mrstefangrimm/Parc/Hardware/Soldering-Scheme-FeatherStack.jpeg

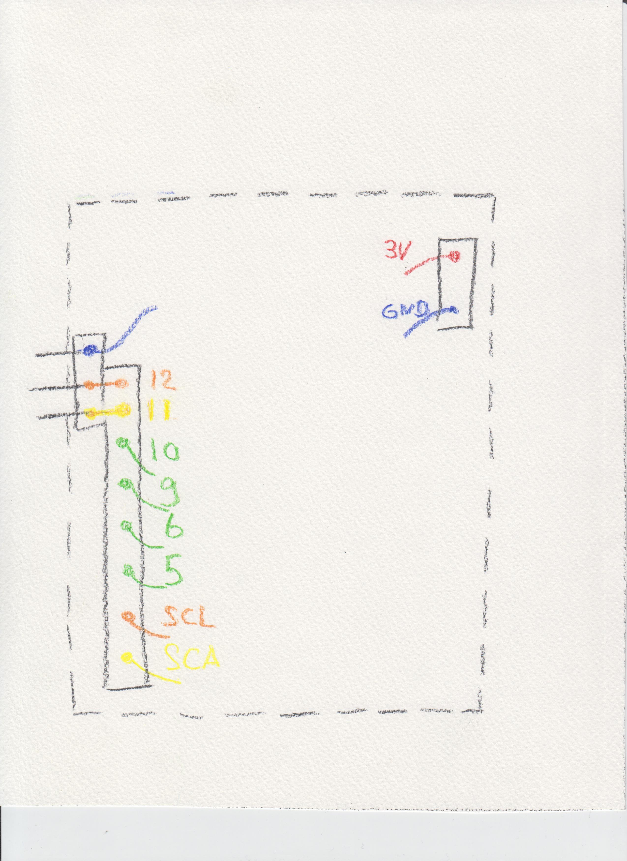
Hardware/Soldering-Scheme-FeatherStack.jpeg
