mrstefangrimm/Parc/Hardware/Soldering-Scheme-Keypad.jpeg

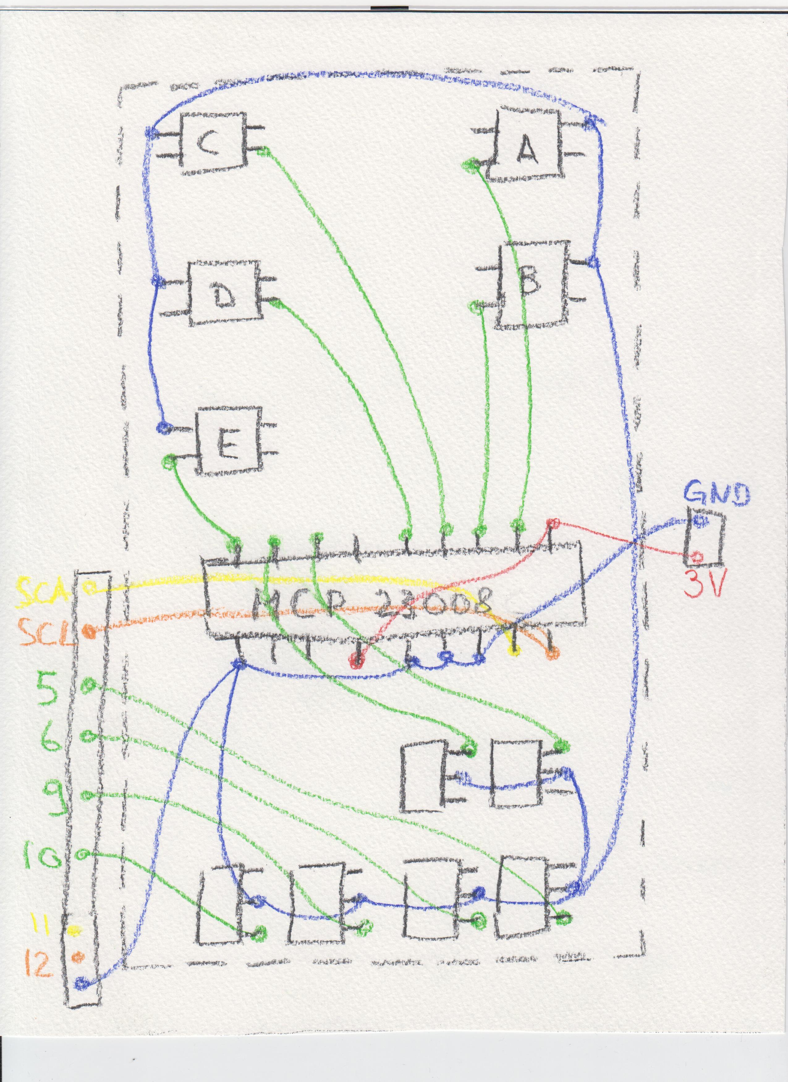
Hardware/Soldering-Scheme-Keypad.jpeg
