mrstefangrimm/Parc/Software/Src/UnoParcApp/Constants.h

// Copyright (c) 2021 Stefan Grimm. All rights reserved.
// Licensed under the LGPL. See LICENSE file in the project root for full license information.
//
#pragma once

namespace unoparc {

// Constants to avoids multiple usage of GPIOs.
// No additional memory is used because of the external constants.

const uint8_t Pin_A = 10;
const uint8_t Pin_B = 9;
const uint8_t Pin_C = 8;
const uint8_t Pin_D = 7;
const uint8_t Pin_E = 6;
const uint8_t Pin_M0 = 5;
const uint8_t Pin_M1 = 0;

const uint8_t Pin_C0 = 0;
const uint8_t Pin_C1 = 0;
const uint8_t Pin_C2 = 0;
const uint8_t Pin_C3 = 0;

const uint8_t Usb_YEL = 11;
const uint8_t Usb_ORA = 12;

}
