mrstefangrimm/Parc/Software/Src/ParcLib/Core/TerminalAo.h

// Copyright (c) 2021-2023 Stefan Grimm. All rights reserved.
// Licensed under the LGPL. See LICENSE file in the project root for full license information.
//
#ifndef PARCLIB_TERMINALAO_H
#define PARCLIB_TERMINALAO_H

#include "Ao.h"
#include "StringParc.h"
#include "Shared.h"
#include "tsm.h"

namespace parclib {

enum PsType {
  Wait,
  UsbKeycode,
  UsbKeycodeRepeated,
  UsbKeycodes,
  UsbText,
  BleKeycode,
  BleKeycodeRepeated,
  BleText,
  BleControlkey
};

enum CmdType {
  _LastStep = BleControlkey,
  Pin
};

template<uint8_t CMDTYPE>
struct CmdComparator {

  bool operator()(const char* another) const {
    return equals(another);
  }
  bool equals(const char* another) const {
    return false;
  }

  bool operator()(char** another) const {
    return equals(another);
  }
  bool equals(char** another) const {
    return false;
  }

};

template<class PROGSTEPFACTORY, class TLOGGERFAC, class KNOWNKEYCODES>
class ProgramStepCreator {
public:
  static ProgramStep<TLOGGERFAC>* createProgramStepWait(const char* delay) {
    uint16_t waitMs = atoi(delay);
    // Debug: _log.print(F("Delay: ")); _log.println(waitMs);

    auto log = TLOGGERFAC::create();
    log->println(F("Create Wait_t"));
    return new Wait_t(waitMs);
  }

  static ProgramStep<TLOGGERFAC>* createProgramStepBleKeyboardCode(char* subStrs[], uint8_t numSubStr) {
    KeyCode keyCode;
    uint8_t repetitions = 0;
    for (int n = 1; n < numSubStr; n++) {
      keyCode.ctrl |= strcmp(subStrs[n], "<Ctrl>") == 0;
      keyCode.shift |= strcmp(subStrs[n], "<Shift>") == 0;
      keyCode.alt |= strcmp(subStrs[n], "<Alt>") == 0;
      keyCode.win |= strcmp(subStrs[n], "<Win>") == 0;

      if (strcmp2("-r", subStrs[n][0], subStrs[n][1])) {
        repetitions = atoi(&subStrs[n][2]);
      }
    }

    auto code = subStrs[numSubStr - 1];
    keyCode.hexCode = strtol(subStrs[numSubStr - 1], 0, KNOWNKEYCODES::BleRadix);
    if (keyCode.hexCode == 0) {
      keyCode.hexCode = symbolToBleKeyode(code);
    }
    auto log = TLOGGERFAC::create();
    //log.print("ProgramStepBleKeyboardCode "); _log.print(hexCode, HEX);
    if (repetitions == 0) {
      log->println(F("Create BleKeycode_t"));
      return new BleKeycode_t(keyCode);
    }
    log->println(F("Create BleKeycodeRepeated_t"));
    return new BleKeycodeRepeated_t(keyCode, repetitions);
  }

  static ProgramStep<TLOGGERFAC>* createProgramStepBleKeyboardText(char* text) {
    auto log = TLOGGERFAC::create();
    //_log.print("TEXT: "); _log.println(text);
    log->println(F("Create BleText_t"));
    return new BleText_t(text);
  }

  static ProgramStep<TLOGGERFAC>* createProgramStepBleControlKey(char* subStrs[], uint8_t numSubStr) {
    auto log = TLOGGERFAC::create();
    // _log.print("Control Key: "); _log.print(subStrs[1]);

    if (strcmp(subStrs[1], "Volume+") == 0) {
      return new BleControlkey_t("0xE9");
    }
    if (strcmp(subStrs[1], "Volume-") == 0) {
      return new BleControlkey_t("0xEA");
    }

    log->println(F("Create BleControlkey_t"));
    return new BleControlkey_t(subStrs[1]);
  }

  static ProgramStep<TLOGGERFAC>* createProgramStepUsbKeyboardCode(char* subStrs[], uint8_t numSubStr) {
    KeyCode keyCode;
    uint8_t repetitions = 0;
    char second = 0;
    for (int n = 1; n < numSubStr; n++) {
      keyCode.ctrl |= strcmp(subStrs[n], "<Ctrl>") == 0;
      keyCode.shift |= strcmp(subStrs[n], "<Shift>") == 0;
      keyCode.alt |= strcmp(subStrs[n], "<Alt>") == 0;
      keyCode.win |= strcmp(subStrs[n], "<Win>") == 0;

      if (strcmp2("-r", subStrs[n][0], subStrs[n][1])) {
        repetitions = atoi(&subStrs[n][2]);
      }
    }

    auto code = subStrs[numSubStr - 1];
    auto log = TLOGGERFAC::create();
    //Debug: _log.print("createProgramStepUsbKeyboardCode "); _log.println(code);

    if (strlen(code) == 3) {
      if (code[0] == '\'' && code[2] == '\'') {
        keyCode.hexCode = code[1];
      }
      else if (repetitions == 0) {
        keyCode.hexCode = code[0];
        second = code[2];
      }
    }
    else {
      keyCode.hexCode = strtol(code, 0, KNOWNKEYCODES::UsbRadix);
    }
    //Debug: _log.print("createProgramStepUsbKeyboardCode "); _log.println(keyCode.hexCode, HEX);
    if (keyCode.hexCode == 0) {
      keyCode.hexCode = symbolToUsbKeyode(code);
    }
    //Debug: _log.print("createProgramStepUsbKeyboardCode "); _log.println(keyCode.hexCode, HEX);
    if (second != 0) {
      log->println(F("Create UsbKeycodes_t"));
      return new UsbKeycodes_t(keyCode, second);
    }
    if (repetitions == 0) {
      log->println(F("Create UsbKeycode_t"));
      return new UsbKeycode_t(keyCode);
    }
    log->println(F("Create UsbKeycodeRepeated_t"));
    return new UsbKeycodeRepeated_t(keyCode, repetitions);
  }

  static ProgramStep<TLOGGERFAC>* createProgramStepUsbKeyboardText(char* text) {
    auto log = TLOGGERFAC::create();
    // log.print("TEXT: "); _log.println(text);
    log->println(F("Create UsbText_t"));
    return new UsbText_t(text);
  }

private:
  using Wait_t = typename TypeAt<PROGSTEPFACTORY, PsType::Wait>::Result;
  using UsbKeycode_t = typename TypeAt<PROGSTEPFACTORY, PsType::UsbKeycode>::Result;
  using UsbKeycodeRepeated_t = typename TypeAt<PROGSTEPFACTORY, PsType::UsbKeycodeRepeated>::Result;
  using UsbKeycodes_t = typename TypeAt<PROGSTEPFACTORY, PsType::UsbKeycodes>::Result;
  using UsbText_t = typename TypeAt<PROGSTEPFACTORY, PsType::UsbText>::Result;
  using BleKeycode_t = typename TypeAt<PROGSTEPFACTORY, PsType::BleKeycode>::Result;
  using BleKeycodeRepeated_t = typename TypeAt<PROGSTEPFACTORY, PsType::BleKeycodeRepeated>::Result;
  using BleText_t = typename TypeAt<PROGSTEPFACTORY, PsType::BleText>::Result;
  using BleControlkey_t = typename TypeAt<PROGSTEPFACTORY, PsType::BleControlkey>::Result;

  static uint8_t symbolToUsbKeyode(const char* code) {
    if (strcmp(code, "<Del>") == 0) {
      return KNOWNKEYCODES::UsbKeyCodeDel;
    }
    if (strcmp(code, "<Tab>") == 0) {
      return KNOWNKEYCODES::UsbKeyCodeTab;
    }
    if (strcmp(code, "<Enter>") == 0) {
      return KNOWNKEYCODES::UsbKeyCodeEnter;
    }
    if (strcmp(code, "<Space>") == 0) {
      return KNOWNKEYCODES::UsbKeyCodeSpace;
    }
    return 0;
  }

  static uint8_t symbolToBleKeyode(const char* code) {
    if (strcmp(code, "<Del>") == 0) {
      return KNOWNKEYCODES::BleKeyCodeDel;
    }
    if (strcmp(code, "<Tab>") == 0) {
      return KNOWNKEYCODES::BleKeyCodeTab;
    }
    if (strcmp(code, "<Enter>") == 0) {
      return KNOWNKEYCODES::BleKeyCodeEnter;
    }
    if (strcmp(code, "<Space>") == 0) {
      return KNOWNKEYCODES::BleKeyCodeSpace;
    }
    return 0;
  }

};

using StatePolicy = tsmlib::State<tsmlib::MemoryAddressComparator, true>;

namespace Trigger {
  struct Timeout {
    void* owner;
  };
  struct InvalidData {
  };
  struct GotPin {
    void* owner;
  };
  struct GotProgramSteps {
    void* owner;
  };
}

// https://viewer.diagrams.net/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

template<class PROGSTEPFACTORY, class TSERIAL, class TLOGGERFAC, class THIDBLEFAC, class THIDUSBFAC, class TPROGRAM, class TSYSTEMHWFAC, class KNOWNKEYCODES, uint8_t BUFLEN>
class TerminalAo : public Ao<TerminalAo<PROGSTEPFACTORY, TSERIAL, TLOGGERFAC, THIDBLEFAC, THIDUSBFAC, TPROGRAM, TSYSTEMHWFAC, KNOWNKEYCODES, BUFLEN>> {

  using Ao_t = Ao<TerminalAo<PROGSTEPFACTORY, TSERIAL, TLOGGERFAC, THIDBLEFAC, THIDUSBFAC, TPROGRAM, TSYSTEMHWFAC, KNOWNKEYCODES, BUFLEN>>;

public:
  TerminalAo(TSERIAL& serialInput, Messages& messages, TPROGRAM* programs)
    : Ao_t(messages), _serial(serialInput), _programs(programs) {
    _statemachine.begin();
  }

  void load() {
    if (_timer.increment()) {
      _msg = TerminalData(Ao_t::_messages.toTerminalQueue.pop());
    }
  }

  void run() {
    if (_timer.current())
    {
      if (_msg.raw == 0 || _msg.isPinMessage) {
        _statemachine.dispatch(Trigger::Timeout{ this });
      }
      else {
        if (_msg.invalidProgramCode)
        {
          _statemachine.dispatch(Trigger::InvalidData{});
        }
        else if (_msg.gotPin)
        {
          _statemachine.dispatch(Trigger::GotPin{ this });
        }
        else if (_msg.gotProgramSteps)
        {
          _statemachine.dispatch(Trigger::GotProgramSteps{ this });
        }
      }

      if (_msg.isPinMessage && _msg.isPinDefined) {
        _serial.println(F("PIN was not accepted. A PIN is already active."));
      }

      _msg = TerminalData();
    }
  }

protected:
  // states
  struct Idle : public tsmlib::BasicState<Idle, StatePolicy, true, false, true>, public tsmlib::SingletonCreator<Idle> {

    bool gotProgramCode = false;

    template<class Event> void entry(const Event&) {
      gotProgramCode = false;
    }

    template<class Event> void doit(const Event& ev) { doit(ev, Identity<Event>()); }
    template<class Event> void doit(const Event&, Identity<Event>) {}
    void doit(const Trigger::Timeout& ev, Identity<Trigger::Timeout>) {
      auto ao = static_cast<TerminalAo*>(ev.owner);
      gotProgramCode = ao->onStateIdleDo();
    }
  };

  struct ReadingProgramCode : public tsmlib::BasicState<ReadingProgramCode, StatePolicy, true, false, true>, public tsmlib::SingletonCreator<ReadingProgramCode> {

    template<class Event> void entry(const Event& ev) { entry(ev, Identity<Event>()); }
    template<class Event> void entry(const Event&, Identity<Event>) {}
    void entry(const Trigger::Timeout& ev, Identity<Trigger::Timeout>) {
      auto ao = static_cast<TerminalAo*>(ev.owner);
      ao->clearReadBuffer();
    }

    template<class Event> void doit(const Event& ev) { doit(ev, Identity<Event>()); }
    template<class Event> void doit(const Event&, Identity<Event>) {}
    void doit(const Trigger::Timeout& ev, Identity<Trigger::Timeout>) {
      auto ao = static_cast<TerminalAo*>(ev.owner);
      ao->onStateReadingProgramCodeDo();
    }
  };

  struct ReadingProgramSteps : public tsmlib::BasicState<ReadingProgramSteps, StatePolicy, true, false, true>, public tsmlib::SingletonCreator<ReadingProgramSteps> {

    bool readingDone = false;

    template<class Event> void entry(const Event& ev) {
      readingDone = false;
      entry(ev, Identity<Event>());
    }
    template<class Event> void entry(const Event&, Identity<Event>) {}
    void entry(const Trigger::GotProgramSteps& ev, Identity<Trigger::GotProgramSteps>) {
      auto ao = static_cast<TerminalAo*>(ev.owner);
      ao->clearReadBuffer();
    }

    template<class Event> void doit(const Event& ev) { doit(ev, Identity<Event>()); }
    template<class Event> void doit(const Event&, Identity<Event>) {}
    void doit(const Trigger::Timeout& ev, Identity<Trigger::Timeout>) {
      auto ao = static_cast<TerminalAo*>(ev.owner);
      readingDone = ao->onStateReadingProgramStepsOnDo();
    }
  };

  struct ReadingPin : public tsmlib::BasicState<ReadingPin, StatePolicy, true, false, true>, public tsmlib::SingletonCreator<ReadingPin> {

    bool readingDone = false;

    template<class Event> void entry(const Event& ev) {
      readingDone = false;
      entry(ev, Identity<Event>());
    }
    template<class Event> void entry(const Event&, Identity<Event>) {}
    void entry(const Trigger::GotPin& ev, Identity<Trigger::GotPin>) {
      auto ao = static_cast<TerminalAo*>(ev.owner);
      ao->clearReadBuffer();
    }

    template<class Event> void doit(const Event& ev) { doit(ev, Identity<Event>()); }
    template<class Event> void doit(const Event&, Identity<Event>) {}
    void doit(const Trigger::Timeout& ev, Identity<Trigger::Timeout>) {
      auto ao = static_cast<TerminalAo*>(ev.owner);
      readingDone = ao->onStateReadingPinDo();
    }
  };

  // guards
  struct ToReadingProgramCodeFromIdleGuard {
    bool eval(const Idle& idle, const Trigger::Timeout&) {
      return idle.gotProgramCode;
    }
  };

  struct ToIdleFromReadingProgramStepsGuard
  {
    bool eval(const ReadingProgramSteps& readingProgramSteps, const Trigger::Timeout&) {
      return readingProgramSteps.readingDone;
    }
  };

  struct ToIdleFromReadingPinGuard
  {
    bool eval(const ReadingPin& readingPin, const Trigger::Timeout&) {
      return readingPin.readingDone;
    }
  };

  using ToReadingProgramCodeFromIdle = tsmlib::ChoiceTransition<Trigger::Timeout, ReadingProgramCode, Idle, Idle, ToReadingProgramCodeFromIdleGuard, tsmlib::NoAction>;
  using ToReadingProgramCodeFromReadingProgramCode = tsmlib::SelfTransition<Trigger::Timeout, ReadingProgramCode, tsmlib::NoGuard, tsmlib::NoAction, false>;
  using ToReadingPinFromReadingProgramCode = tsmlib::Transition<Trigger::GotPin, ReadingPin, ReadingProgramCode, tsmlib::NoGuard, tsmlib::NoAction>;
  using ToReadingProgramStepsFromProgramCode = tsmlib::Transition<Trigger::GotProgramSteps, ReadingProgramSteps, ReadingProgramCode, tsmlib::NoGuard, tsmlib::NoAction>;
  using ToIdleFromProgramCode = tsmlib::Transition<Trigger::InvalidData, Idle, ReadingProgramCode, tsmlib::NoGuard, tsmlib::NoAction>;

  using ToIdleFromReadingProgramSteps = tsmlib::ChoiceTransition<Trigger::Timeout, Idle, ReadingProgramSteps, ReadingProgramSteps, ToIdleFromReadingProgramStepsGuard, tsmlib::NoAction>;
  using ToIdleFromReadingPin = tsmlib::ChoiceTransition<Trigger::Timeout, Idle, ReadingPin, ReadingPin, ToIdleFromReadingPinGuard, tsmlib::NoAction>;

  using Transitions =
    tsmlib::Typelist<ToReadingProgramCodeFromIdle,
    tsmlib::Typelist<ToReadingProgramCodeFromReadingProgramCode,
    tsmlib::Typelist<ToReadingPinFromReadingProgramCode,
    tsmlib::Typelist<ToReadingProgramStepsFromProgramCode,
    tsmlib::Typelist<ToIdleFromProgramCode,
    tsmlib::Typelist<ToIdleFromReadingProgramSteps,
    tsmlib::Typelist<ToIdleFromReadingPin,
    tsmlib::NullType>>>>>>>;

  // state machine
  using InitTransition = tsmlib::InitialTransition<Idle, tsmlib::NoAction>;
  using SM_t = tsmlib::Statemachine<Transitions, InitTransition>;
  SM_t _statemachine;

  TSERIAL& _serial;
  BitCounter<0> _timer;
  TerminalData _msg;

  bool onStateIdleDo() {
    char ch = 0;
    while (_serial.available()) {
      ch = _serial.read();
      if (ch == '{') {
        // send blocked to KeypadAo
        _serial.print(F("> {"));
        return true;
      }
      else if (ch == '?') {
        _serial.println(F("Programmed:"));
        for (int m = 0; m < 4; m++) {
          for (int n = 1; n < 6; n++) {
            KeypadRegData input(m, n);
            _serial.print(input.mode); _serial.print(F(" ")); _serial.print(char(input.button - 1 + 'A')); _serial.print(F(" : "));
            _programs[input.programIndex()].hasSteps() ? _serial.println(F("Yes")) : _serial.println(F("No"));
          }
        }
        auto sysHw = TSYSTEMHWFAC::create();
        _serial.print(F("Remaining bytes: ")); _serial.println(sysHw->freeMemory());
        return false;
      }
      else if (isprint(ch)) {
        _serial.print(ch);
      }
    }
    if (ch != 0 /*&& ch != 0b1101 && ch != 0b1010*/) {
      // YAT sends 0b1101 and 0b1010, PuTTY sends 0b1101 and powershell sends 0b1010
      // Debug: Serial.println("Enter pressed");
      // Debug: Serial.println(); //eol of repeated command
      _serial.println(F("Start defining your dull programs."));
    }
    return false;
  }

  void onStateReadingProgramCodeDo() {
    auto log = TLOGGERFAC::create();

    while (_serial.available()) {
      char ch = _serial.read();
      _serial.print(ch);
      if (ch == ':') {
        parclib::trimFront(_buf);
        parclib::trimBack(_buf, BUFLEN);
        parclib::squeeze(_buf);
        // Debug: _serial.println(_buf);
        uint8_t numSubStr;
        char* subStrs[2] = { 0 };
        parclib::split(_buf, BUFLEN, ' ', subStrs, &numSubStr);

        if (numSubStr == 2) {
          if (CmdComparator<CmdType::Pin>()(subStrs)) {
            _keyPadInput.isPin = 1;
          }
          else {
            // Debug: _serial.println(subStrs[0][0]); // Does not work when backspace is used in putty
            // Debug: _serial.println(subStrs[1][0]); // Does not work when backspace is used in putty
            // Debug: _serial.println(subStrs[0][strlen(subStrs[0])-1]);
            // Debug: _serial.println(subStrs[1][strlen(subStrs[1])-1]);

            _keyPadInput.isPin = 0;
            _keyPadInput.mode = subStrs[0][0] - '0';
            _keyPadInput.button = subStrs[1][0] - 'A' + 1;

            // Debug: _serial.println(_keyPadInput.mode);
            // Debug: _serial.println(_keyPadInput.button);
          }
        }

        if (_keyPadInput.isPin) {
          log->println(F("got pin"));
          TerminalData msg;
          msg.gotPin = true;
          Ao_t::_messages.toTerminalQueue.push(msg.raw);
          return;
        }
        auto idx = _keyPadInput.programIndex();
        // Debug: _log.print(_keyPadInput.mode); _log.print(F(" ")); _log.print(_keyPadInput.button); _log.print(F(" > ")); _log.println(idx);
        if (0 <= idx && idx < NumberOfPrograms) {
          TPROGRAM& prog = _programs[idx];
          if (prog.hasSteps()) {
            log->println(F("got program index. Current program is being disposed."));
          }
          prog.dispose();
          TerminalData msg;
          msg.gotProgramSteps = true;
          Ao_t::_messages.toTerminalQueue.push(msg.raw);
          return;
        }
        _serial.println(F(" This ain't dull, bye."));
        TerminalData msg;
        msg.invalidProgramCode = true;
        Ao_t::_messages.toTerminalQueue.push(msg.raw);
      }
      else if (_itBuf < BUFLEN) {
        // omit preceding spaces to save the buffer for the data.
        if (_itBuf > 0 || ch != ' ') {
          _buf[_itBuf] = ch;
          _itBuf++;
        }
      }
    }
  }

  bool onStateReadingPinDo() {
    // Debug:auto log = TLOGGERFAC::create();

    while (_serial.available()) {
      char ch = _serial.read();
      _serial.print(ch);
      // Debug: log->print(ch);

      if (ch == '}') {
        _serial.println(F(", thank you."));
        // Debug: log->println(F(", thank you."));

        return true;
        // send unblocked to KeypadAo
      }
      else if (ch == ';') {
        // create programstep. If failed, go to wait state
        // Debug: log->print(_buf);
        parclib::trimFront(_buf);
        parclib::trimBack(_buf, BUFLEN);
        parclib::squeeze(_buf);
        uint8_t numSubStr;
        char* subStrs[6] = { 0 };
        parclib::split(_buf, BUFLEN, ' ', subStrs, &numSubStr);

        if (numSubStr != 5) {
          _serial.println(F(" This ain't dull, bye."));
          // Debug: log->print(F(" This ain't dull, bye."));
          return true;
        }
        PinRegData pin;
        pin.code3 = subStrs[0][0] == '1' ? 1 : 0;
        pin.code2 = subStrs[1][0] == '1' ? 1 : 0;
        pin.code1 = subStrs[2][0] == '1' ? 1 : 0;
        pin.code0 = subStrs[3][0] == '1' ? 1 : 0;
        pin.retries = atoi(subStrs[4]);

        // Pin is sent before the command is completed with '}'
        Ao_t::_messages.fromTerminalToKeypadQueue.push(pin.raw);
      }
      else if (_itBuf < BUFLEN) {
        // omit preceding spaces to save the buffer for the data.
        if (_itBuf > 0 || ch != ' ') {
          _buf[_itBuf] = ch;
          _itBuf++;
        }
      }
    }
    return false;
  }

  bool onStateReadingProgramStepsOnDo() {
    while (_serial.available()) {
      char ch = _serial.read();
      _serial.print(ch);
      if (ch == '}') {
        _serial.println(F(", thank you."));
        Ao_t::_messages.fromTerminalToServiceMonitorQueue.push(ProgramChangedRegData(1));
        // send unblocked to KeypadAo
        return true;
      }
      else if (ch == ';') {
        // create programstep. If failed, go to wait state
        parclib::trimFront(_buf);
        parclib::trimBack(_buf, BUFLEN);
        parclib::squeeze(_buf);
        // Debug: _serial.println(_buf);

        uint8_t numSubStr;
        char* subStrs[6] = { 0 };
        parclib::split(_buf, BUFLEN, ' ', subStrs, &numSubStr);

        ProgramStep<TLOGGERFAC>* progStep = 0;

        if (CmdComparator<PsType::Wait>()(subStrs[0])) {
          progStep = ProgramStepCreator<PROGSTEPFACTORY, TLOGGERFAC, KNOWNKEYCODES>::createProgramStepWait(subStrs[1]);
        }
        else if (CmdComparator<PsType::BleKeycode>()(subStrs[0])) {
          progStep = ProgramStepCreator<PROGSTEPFACTORY, TLOGGERFAC, KNOWNKEYCODES>::createProgramStepBleKeyboardCode(subStrs, numSubStr);
        }
        else if (CmdComparator<PsType::BleText>()(subStrs[0])) {
          progStep = ProgramStepCreator<PROGSTEPFACTORY, TLOGGERFAC, KNOWNKEYCODES>::createProgramStepBleKeyboardText(subStrs[1]);
        }
        else if (CmdComparator<PsType::BleControlkey>()(subStrs[0])) {
          progStep = ProgramStepCreator<PROGSTEPFACTORY, TLOGGERFAC, KNOWNKEYCODES>::createProgramStepBleControlKey(subStrs, numSubStr);
        }
        else if (CmdComparator<PsType::UsbKeycode>()(subStrs[0])) {
          progStep = ProgramStepCreator<PROGSTEPFACTORY, TLOGGERFAC, KNOWNKEYCODES>::createProgramStepUsbKeyboardCode(subStrs, numSubStr);
        }
        else if (CmdComparator<PsType::UsbText>()(subStrs[0])) {
          progStep = ProgramStepCreator<PROGSTEPFACTORY, TLOGGERFAC, KNOWNKEYCODES>::createProgramStepUsbKeyboardText(subStrs[1]);
        }

        if (progStep != 0) {
          uint8_t progIdx = _keyPadInput.programIndex();
          _programs[progIdx].appendStep(progStep);

          // Steps remaining.
          clearReadBuffer();
          return false;
        }

        _serial.println(F(" Unknown command. This ain't dull, bye."));
        // Remove the already processed program steps from the program.
        uint8_t progIdx = _keyPadInput.programIndex();
        _programs[progIdx].dispose();
        return true;
      }
      else if (_itBuf < BUFLEN) {
        // omit preceding spaces to save the buffer for the data.
        if (_itBuf > 0 || ch != ' ') {
          _buf[_itBuf] = ch;
          _itBuf++;
        }
      }
      else {
        _serial.println(F(" Command string too long. This ain't dull, bye."));
        // Remove the already processed program steps from the program.
        uint8_t progIdx = _keyPadInput.programIndex();
        _programs[progIdx].dispose();
        return true;
      }
    }
    return false;
  }

  void clearReadBuffer() {
    _itBuf = 0;
    memset(_buf, 0, BUFLEN);
  }

  TPROGRAM* _programs;

  char _buf[BUFLEN] = { 0 };
  uint8_t _itBuf = 0;

  KeypadRegData _keyPadInput;

};

}

#endif
