mrstefangrimm/Parc/Software/ParcApp/TerminalAo.h

// Copyright (c) 2021 Stefan Grimm. All rights reserved.
// Licensed under the LGPL. See LICENSE file in the project root for full license information.
//
#pragma once

#include "Ao.h"
#include "StringAlgo.h"
#include "Shared.h"

namespace parc {

  enum PsType {
    Wait,
    UsbKeycode,
    UsbText,
    BleKeycode,
    BleText,
    BleControlkey
  };

  template<uint8_t CMDTYPE>
  struct CmdComparator {

    bool operator()(const char* another) {
      return equals(another);
    }
    bool equals(const char* another) { return false; }
  };


  template<typename PROGSTEPFACTORY, class TSERIAL, class TLOGGER, class THIDBLE, class THIDUSB, uint8_t BUFLEN>
  class TerminalAo : public Ao<TerminalAo<PROGSTEPFACTORY, TSERIAL, TLOGGER, THIDBLE, THIDUSB, BUFLEN>> {
  public:
    TerminalAo(TSERIAL& serialInput, TLOGGER& logger, THIDBLE& ble, THIDUSB& usb, RegisterData_t* registers, Program<TLOGGER>* programs)
      : Ao_t(registers), _serial(serialInput), _state(State::Idle), _log(logger), _ble(ble), _usb(usb), _programs(programs) {}

    void checkRegisters() {
      if (Ao_t::_registers[TERMINAL_TERMINAL_TIMEOUT] != 0) {
        switch (_state) {
          case State::Idle: stateIdle(); break;
          case State::ReadingProgramCode: stateReadingProgramCode(); break;
          case State::ReadingProgramSteps: stateReadingProgramSteps(); break;
          case State::ReadingPin: stateReadingPin(); break;
        };

        Ao_t::_registers[TERMINAL_TERMINAL_TIMEOUT] = TimerRegData(1);
      }

      if (Ao_t::_registers[KEYPAD_TERMINAL_PINALREADYDEFINED] != 0) {
        _serial.println(F("PIN was not accepted. A PIN is already active."));
        Ao_t::_registers[KEYPAD_TERMINAL_PINALREADYDEFINED] = 0;
      }
    }

  private:
    void stateIdle() {
      char ch = 0;
      while (_serial.available() && _state == State::Idle) {
        ch = _serial.read();
        if (ch == '{') {
          // send blocked to KeypadAo
          _serial.print(F("> {"));

          _itBuf = 0;
          memset(_buf, 0, BUFLEN);
          ch = 0;
          _state = State::ReadingProgramCode;
        }
        else if (ch == '?') {
          _serial.println(F("Programmed:"));
          for (int m = 0; m < 4; m++) {
            for (int n = 1; n < 6; n++) {
              KeypadRegData input(m, n);
              _serial.print(input.profile); _serial.print(F(" ")); _serial.print(char(input.button - 1 + 'A')); _serial.print(F(" : "));
              _programs[input.programIndex()].hasSteps() ? _serial.println(F("Yes")) : _serial.println(F("No"));
            }
          }
         
        }
        else if (isprint(ch)) {
          _serial.print(ch);
        }        
      }
      if (ch != 0 /*&& ch != 0b1101 && ch != 0b1010*/) {
        // YAT sends 0b1101 and 0b1010, PuTTY sends 0b1101 and powershell sends 0b1010
        // Debug: Serial.println("Enter pressed");
        // Debug: Serial.println(); //eol of repeated command
        _serial.println(F("Start defining your dull programs."));
      }
    }

    void stateReadingProgramCode() {
      while (_serial.available() && _state == State::ReadingProgramCode) {
        char ch = _serial.read();
        _serial.print(ch);
        if (ch == ':') {
          parc::trimFront(_buf, BUFLEN);
          parc::trimBack(_buf, BUFLEN);
          parc::squeeze(_buf);
          // Debug: _serial.println(_buf);
          uint8_t numSubStr;
          char* subStrs[2] = { 0 };
          parc::split(_buf, BUFLEN, ' ', subStrs, &numSubStr);          

          if (numSubStr == 2) {
            if (subStrs[0][0] == 'P' && subStrs[1][0] == 'N') {
              _keyPadState.isPin = 1;
            }
            else {              
              // Debug: _serial.println(subStrs[0][0]); // Does not work when backspace is used in putty
              // Debug: _serial.println(subStrs[1][0]); // Does not work when backspace is used in putty
              // Debug: _serial.println(subStrs[0][strlen(subStrs[0])-1]);
              // Debug: _serial.println(subStrs[1][strlen(subStrs[1])-1]);
          
              _keyPadState.isPin = 0;
              _keyPadState.profile = subStrs[0][0] - '0';
              _keyPadState.button = subStrs[1][0] - 'A' + 1;

              // Debug: _serial.println(_keyPadState.profile);
              // Debug: _serial.println(_keyPadState.button);
            }
          }

          _itBuf = 0;
          memset(_buf, 0, BUFLEN);

          if (_keyPadState.isPin) {
            _log.println(F("got pin"));
            _state = State::ReadingPin;
          }
          else {
            auto idx = _keyPadState.programIndex();
            // Debug: _log.print(_keyPadState.profile); _log.print(F(" ")); _log.print(_keyPadState.button); _log.print(F(" > ")); _log.println(idx);
            if (0 <= idx && idx < NumberOfPrograms) {
              _log.println(F("got program index. Current program is being disposed."));
              _state = State::ReadingProgramSteps;
              _programs[idx].dispose();
            }
            else {
              _serial.println(F(" This ain't dull, bye."));
              _state = State::Idle;
            }
          }    
        }
        else if (_itBuf < BUFLEN) {
          // omit preceding spaces to save the buffer for the data.
          if (_itBuf > 0 || ch != ' ') {
            _buf[_itBuf] = ch;
            _itBuf++;
          }
        }
      }
    }

    void stateReadingPin() {
      while (_serial.available() && _state == State::ReadingPin) {
        char ch = _serial.read();
        _serial.print(ch);
        if (ch == '}') {
          _serial.println(F(", thank you."));
          _state = State::Idle;
          // send unblocked to KeypadAo
        }
        else if (ch == ';') {
          // create programstep. If failed, go to wait state
          //_log.print(_buf);
          parc::trimFront(_buf, BUFLEN);
          parc::trimBack(_buf, BUFLEN);
          parc::squeeze(_buf);
          uint8_t numSubStr;
          char* subStrs[6] = { 0 };
          parc::split(_buf, BUFLEN, ' ', subStrs, &numSubStr);

          if (numSubStr == 5) {
            PinRegData pin;
            pin.code3 = subStrs[0][0] == '1' ? 1 : 0;
            pin.code2 = subStrs[1][0] == '1' ? 1 : 0;
            pin.code1 = subStrs[2][0] == '1' ? 1 : 0;
            pin.code0 = subStrs[3][0] == '1' ? 1 : 0;
            pin.retries = atoi(subStrs[4]);

            Ao<TerminalAo<PROGSTEPFACTORY, TSERIAL, TLOGGER, THIDBLE, THIDUSB, BUFLEN>>::_registers[TERMINAL_KEYPAD_PIN] = pin.raw;
          }
          else {
            _serial.println(F(" This ain't dull, bye."));
            _state = State::Idle;
          }
          _itBuf = 0;
          memset(_buf, 0, BUFLEN);
        }
        else if (_itBuf < BUFLEN) {
          // omit preceding spaces to save the buffer for the data.
          if (_itBuf > 0 || ch != ' ') {
            _buf[_itBuf] = ch;
            _itBuf++;
          }
        }
      }
    }

    void stateReadingProgramSteps() {
      while (_serial.available() && _state == State::ReadingProgramSteps) {
        char ch = _serial.read();
        _serial.print(ch);
        if (ch == '}') {
          _serial.println(F(", thank you."));
          _state = State::Idle;
          // send unblocked to KeypadAo
        }
        else if (ch == ';') {
          // create programstep. If failed, go to wait state
          parc::trimFront(_buf, BUFLEN);
          parc::trimBack(_buf, BUFLEN);
          parc::squeeze(_buf);
          // Debug: _serial.println(_buf);
          
          uint8_t numSubStr;
          char* subStrs[6] = { 0 };
          parc::split(_buf, BUFLEN, ' ', subStrs, &numSubStr);

          ProgramStep<TLOGGER>* progStep = 0;
         
          if (CmdComparator<PsType::Wait>()(subStrs[0])) {
            progStep = createProgramStepWait(subStrs[1]);
          }
          else if (CmdComparator<PsType::BleKeycode>()(subStrs[0])) {
            progStep = createProgramStepBleKeyboardCode(subStrs, numSubStr);
          }
          else if (CmdComparator<PsType::BleText>()(subStrs[0])) {
            progStep = createProgramStepBleKeyboardText(subStrs[1]);
          }
          else if (CmdComparator<PsType::BleControlkey>()(subStrs[0])) {
            progStep = createProgramStepBleControlKey(subStrs, numSubStr);
          }
          else if (CmdComparator<PsType::UsbKeycode>()(subStrs[0])) {
            progStep = createProgramStepUsbKeyboardCode(subStrs, numSubStr);
          }
          else if (CmdComparator<PsType::UsbText>()(subStrs[0])) {
            progStep = createProgramStepUsbKeyboardText(subStrs[1]);
          }

          if (progStep != 0) {
            uint8_t progIdx = _keyPadState.programIndex();
            _programs[progIdx].appendStep(progStep);
            Ao<TerminalAo<PROGSTEPFACTORY, TSERIAL, TLOGGER, THIDBLE, THIDUSB, BUFLEN>>::_registers[TERMINAL_MEMORY_CHANGE] = MemoryChangedRegData(1);
          }
          else {
            _serial.println(F(" Unknown command. This ain't dull, bye."));
            uint8_t progIdx = _keyPadState.programIndex();
            _programs[progIdx].dispose();
            _state = State::Idle;
          }

          _itBuf = 0;
          memset(_buf, 0, BUFLEN);
        }
        else if (_itBuf < BUFLEN) {
          // omit preceding spaces to save the buffer for the data.
          if (_itBuf > 0 || ch != ' ') {
            _buf[_itBuf] = ch;
            _itBuf++;
          }
        }
      }
    }

    ProgramStep<TLOGGER>* createProgramStepWait(const char* delay) {
      uint16_t waitMs = atoi(delay);
      _log.print("DELAY: "); _log.println(waitMs);
      
      return new Wait_t(_log, waitMs);
    }

    ProgramStep<TLOGGER>* createProgramStepBleKeyboardCode(char* subStrs[], uint8_t numSubStr) {
      KeyCode keyCode;
      for (int n = 1; n < numSubStr; n++) {
        keyCode.ctrl |= strcmp(subStrs[n], "<Ctrl>") == 0;
        keyCode.shift |= strcmp(subStrs[n], "<Shift>") == 0;
        keyCode.alt |= strcmp(subStrs[n], "<Alt>") == 0;
        keyCode.win |= strcmp(subStrs[n], "<Win>") == 0;
      }

      keyCode.hexCode = strtol(subStrs[numSubStr - 1], 0, 16);
      keyCode.hexCode = keyCode.hexCode == 0 ? strcmp(subStrs[numSubStr - 1], "<Del>") == 0 ? 0x4C : keyCode.hexCode : keyCode.hexCode;
      keyCode.hexCode = keyCode.hexCode == 0 ? strcmp(subStrs[numSubStr - 1], "<Enter>") == 0 ? 0x28 : keyCode.hexCode : keyCode.hexCode;
      keyCode.hexCode = keyCode.hexCode == 0 ? strcmp(subStrs[numSubStr - 1], "<Tab>") == 0 ? 0x2B : keyCode.hexCode : keyCode.hexCode;
      keyCode.hexCode = keyCode.hexCode == 0 ? strcmp(subStrs[numSubStr - 1], "<Space>") == 0 ? 0x2C : keyCode.hexCode : keyCode.hexCode;

      //_log.print("ProgramStepBleKeyboardCode "); _log.print(hexCode, HEX);
      return new BleKeycode_t(_log, _ble, keyCode);
    }

    ProgramStep<TLOGGER>* createProgramStepBleKeyboardText(char* text) {
      //_log.print("TEXT: "); _log.println(text);
      return new BleText_t(_log, _ble, text);
    }

    ProgramStep<TLOGGER>* createProgramStepBleControlKey(char* subStrs[], uint8_t numSubStr) {
      auto duration = numSubStr > 2 ? atoi(subStrs[2]) : 1;
      // _log.print("Control Key: "); _log.print(subStrs[1]); _log.print(" for: "); _log.println(duration);   

      if (strcmp(subStrs[1], "Volume+") == 0) { return new BleControlkey_t(_log, _ble, "0xE9", duration); }
      if (strcmp(subStrs[1], "Volume-") == 0) { return new BleControlkey_t(_log, _ble, "0xEA", duration); }
      return new BleControlkey_t(_log, _ble, subStrs[1], duration);
    }

    ProgramStep<TLOGGER>* createProgramStepUsbKeyboardCode(char* subStrs[], uint8_t numSubStr) {
      KeyCode keyCode;
      for (int n = 1; n < numSubStr; n++) {
        keyCode.ctrl |= strcmp(subStrs[n], "<Ctrl>") == 0;
        keyCode.shift |= strcmp(subStrs[n], "<Shift>") == 0;
        keyCode.alt |= strcmp(subStrs[n], "<Alt>") == 0;
        keyCode.win |= strcmp(subStrs[n], "<Win>") == 0;
      }

      keyCode.hexCode = strtol(subStrs[numSubStr - 1], 0, 16); // 0x0;
      auto code = subStrs[numSubStr - 1];
      if (strlen(code) == 3 && code[0] == '\'' && code[2] == '\'') {
        keyCode.hexCode = code[1];
      }
      keyCode.hexCode = keyCode.hexCode == 0 ? strcmp(subStrs[numSubStr - 1], "<Del>") == 0 ? 0xD4 : keyCode.hexCode : keyCode.hexCode;
      keyCode.hexCode = keyCode.hexCode == 0 ? strcmp(subStrs[numSubStr - 1], "<Enter>") == 0 ? 0xB0 : keyCode.hexCode : keyCode.hexCode;
      keyCode.hexCode = keyCode.hexCode == 0 ? strcmp(subStrs[numSubStr - 1], "<Tab>") == 0 ? 0xB3 : keyCode.hexCode : keyCode.hexCode;
      keyCode.hexCode = keyCode.hexCode == 0 ? strcmp(subStrs[numSubStr - 1], "<Space>") == 0 ? ' ' : keyCode.hexCode : keyCode.hexCode;

      // _log.print("createProgramStepUsbKeyboardCode "); _log.print(hexCode, HEX);
      return new UsbKeycode_t(_log, _usb, keyCode);
    }

    ProgramStep<TLOGGER>* createProgramStepUsbKeyboardText(char* text) {
      // _log.print("TEXT: "); _log.println(text);
      return new UsbText_t(_log, _usb, text);
    }
    
  private:
    typedef Ao<TerminalAo<PROGSTEPFACTORY, TSERIAL, TLOGGER, THIDBLE, THIDUSB, BUFLEN>> Ao_t;
    typedef typename TypeAt<PROGSTEPFACTORY, PsType::Wait>::Result Wait_t;
    typedef typename TypeAt<PROGSTEPFACTORY, PsType::BleKeycode>::Result BleKeycode_t;
    typedef typename TypeAt<PROGSTEPFACTORY, PsType::BleText>::Result BleText_t;
    typedef typename TypeAt<PROGSTEPFACTORY, PsType::BleControlkey>::Result BleControlkey_t;
    typedef typename TypeAt<PROGSTEPFACTORY, PsType::UsbKeycode>::Result UsbKeycode_t;
    typedef typename TypeAt<PROGSTEPFACTORY, PsType::UsbText>::Result UsbText_t;

    enum class State {
      Blocked,
      Idle,
      ReadingProgramCode,
      ReadingProgramSteps,
      ReadingPin
    };
    State _state;
    TSERIAL& _serial;
    TLOGGER& _log;
    THIDBLE& _ble;
    THIDUSB& _usb;
    Program<TLOGGER>* _programs;

    char _buf[BUFLEN] = { 0 };
    uint8_t _itBuf = 0;

    KeypadRegData _keyPadState;

  };

}
