mrstefangrimm/Parc/Software/Src/ParcLib/Core/HidAo.h

// Copyright (c) 2021-2023 Stefan Grimm. All rights reserved.
// Licensed under the LGPL. See LICENSE file in the project root for full license information.
//
#ifndef PARCLIB_HIDAO_H
#define PARCLIB_HIDAO_H

#include "Ao.h"
#include "BitCounter.h"
#include "ProgramStep.h"
#include "Program.h"

namespace parclib {

template<class TLOGGERFAC, class TPROGRAM>
class HidAo : public Ao<HidAo<TLOGGERFAC, TPROGRAM>> {

  public:
    HidAo(Messages& messages, TPROGRAM* programs)
      : Ao_t(messages), _programs(programs) {}

    TPROGRAM* programs() {
      return _programs;
    }

    void load() {
      if (_timer.increment()) {
        _inputMsg = Ao_t::_messages.fromKeypadToHidQueue.pop();
      }
    }

    void run() {
      if (_timer.current()) {
        switch (_state) {
        case State::Idle: stateIdle(_inputMsg); break;
        case State::Execute: stateExecute(); break;
        };
        _inputMsg = 0;
      }
    }

  private:
    void stateIdle(MessageData_t inputMsg) {
      if (inputMsg != 0) {

        KeypadRegData args(inputMsg);
        uint8_t progIdx = args.programIndex();
        _program = &_programs[progIdx];
        _ticksRemaining = _program->duration();

        auto log = TLOGGERFAC::create();
        log->print(F("HidAo:stateIdle() Received Mode: ")); log->print(args.mode); log->print(F(" Button: ")); log->print(args.button);
        log->print(F(" Prog. ")); log->print(progIdx); log->print(F(" Duration: ")); log->println(_ticksRemaining);

        // State Execute if a program is defined. `_ticksRemaining > 0` is equivalent to `_program.hasSteps()`
        if (_ticksRemaining > 0) {
          log->print(F("Execute { "));
          _state = State::Execute;
        }
      }
    }

    void stateExecute() {

      _ticksRemaining--;
      _program->play();

      if (_ticksRemaining == 0) {
        auto log = TLOGGERFAC::create();
        log->println(F("}"));
        _program->rewind();
        _program = 0;
        _state = State::Idle;
      }
    }

  private:
    using Ao_t = Ao<HidAo<TLOGGERFAC, TPROGRAM>>;

    TPROGRAM* _programs = nullptr;

    enum class State {
      Idle,
      Execute
    };
    State _state = State::Idle;
    TPROGRAM* _program = nullptr;
    size_t _ticksRemaining = 0;
    BitCounter<0> _timer;
    MessageData_t _inputMsg = 0;
};

}

#endif
