mrstefangrimm/Parc/Software/Src/ParcLib/Core/Shared.h

// Copyright (c) 2021-2023 Stefan Grimm. All rights reserved.
// Licensed under the LGPL. See LICENSE file in the project root for full license information.
//
#ifndef PARCLIB_SHARED_H
#define PARCLIB_SHARED_H

namespace parclib {

// Intervals per ActiveObject (BSP_Tick)
const uint8_t TimerPeriod = 100;
// TODO: main loop must have a sleep for the defined value.
//const uint8_t TimerPeriod = 125;

// Given by 5 buttons (A-E) and 4 modes (0-3)
const uint8_t NumberOfPrograms = 20;

enum KeyPadSwitch {
  Btn_A,
  Btn_B,
  Btn_C,
  Btn_D,
  Btn_E,
  Sw_M0,
  Sw_M1,
  Code_1,
  Code_2,
  Code_3,
  Code_4
};

// Should it be in this file?
// 20210209 - having hexCode in a separate argument uses the same amount of memory.
struct KeyCode {
  KeyCode() : raw(0) {}
  KeyCode(const KeyCode& t) : raw(t.raw) {}
  KeyCode(uint16_t rawValue) : raw(rawValue) {}

  union {
    struct {
      uint16_t hexCode : 8;
      uint16_t ctrl    : 1;
      uint16_t shift   : 1;
      uint16_t alt     : 1;
      uint16_t win     : 1;
    };
    uint16_t raw;
  };
};

template <class T>
struct Factory {

  static T* create() {
    return &instance;
  }

  static T& instance;
};

// From Modern C++
template<uint8_t V>
struct Int2Type {
  enum { value = V };
};

// From Modern C++
class NullType {};

// From Modern C++
template<class T, typename U>
struct Typelist {
  typedef T Head;
  typedef U Tail;
};

// From Modern C++
template<class TL, uint8_t INDEX> struct TypeAt;
template<class HEAD, class TAIL>
struct TypeAt<Typelist<HEAD, TAIL>, 0>
{
  typedef HEAD Result;
};
template<class HEAD, class TAIL, uint8_t INDEX>
struct TypeAt<Typelist<HEAD, TAIL>, INDEX>
{
  typedef typename TypeAt < TAIL, INDEX - 1 >::Result Result;
};

// From Modern C++
//template<class TLIST, class T> struct IndexOf;
//template<class T>
//struct IndexOf<NullType, T> {
//  enum { Result = -1 };
//};
//template<class T, class TAIL>
//struct IndexOf<Typelist<T, TAIL>, T> {
//  enum { Result = 0 };
//};
//template<class HEAD, class TAIL, class T>
//struct IndexOf<Typelist<HEAD, TAIL>, T> {
//private:
//  enum { Temp = IndexOf<TAIL, T>::Result };
//public:
//  enum { Result = Temp == -1 ? -1 : 1 + Temp };
//};

// From Stackoverflow
template<typename T>
struct Identity { typedef T type; };

}

#endif
