mrstefangrimm/Parc/Software/Src/ParcLib/Core/ValueQueue.h

// Copyright (c) 2023 Stefan Grimm. All rights reserved.
// Licensed under the LGPL. See LICENSE file in the project root for full license information.
//
#ifndef PARCLIB_VALUEQUEUE_H
#define PARCLIB_VALUEQUEUE_H

void rtassert(bool condition);

namespace parclib {

  // ItemAlloc, pop return false?
  template<size_t size, class ItemType = uint8_t>
  class ValueQueue {
  public:
    void push(ItemType item) {
      //static_assert(false, "Only queue size 1 and 2 is supported");
    }
    ItemType pop() {
      return 0;
    }
  };

  template<class ItemType>
  class ValueQueue<0, ItemType> {
  public:
    void push(ItemType item) {
      //static_assert(false, "Only queue size 1 and 2 is supported");
    }
    ItemType pop() {
      return 0;
    }
  private:
    ItemType _item = 0;
  };

  template<class ItemType>
  class ValueQueue<1, ItemType> {
  public:
    void push(ItemType item) {
      rtassert(_item == 0);
      _item = item;
    }
    ItemType pop() {
      ItemType ret = _item;
      _item = 0;
      return ret;
    }
  private:
    ItemType _item = 0;
  };

  template<class ItemType>
  class ValueQueue<2, ItemType> {
  public:
    void push(ItemType item) {
      rtassert(_item1 == 0 || _item2 == 0);
      if (_item1 == 0) {
        _item1 = item;
      }
      else {
        _item2 = item;
      }

    }
    ItemType pop() {
      ItemType ret = _item1;
      _item1 = _item2;
      _item2 = 0;
      return ret;
    }
  private:
    ItemType _item1 = 0;
    ItemType _item2 = 0;
  };
}

#endif
