mrstefangrimm/Parc/Software/Src/ParcLib/Tests/Core/TerminalAoTest/TerminalAoCommandsTest/TerminalAoCommandsTest.ino

// Copyright (c) 2023 Stefan Grimm. All rights reserved.
// Licensed under the LGPL. See LICENSE file in the project root for full license information.
//

#line 6 "basic.ino"
#include <ArduinoUnit.h>
#include <StandardCplusplus.h>  // Commented out all code in new_handler.cpp is commented out. This fix did not work: https://github.com/mike-matera/ArduinoSTL/issues/66 (ArduinoSTL does not create output, so I used StandardCplusplus)
#include "ParcLib.h"
#include "Tests/NotquiteBDD.h"
#include "Tests/Core/TerminalAoTest/TerminalAoTestShared.h"

void rtassert(bool condition) {
  TRUE(condition);
}

#include "TerminalAoCommandsTest.h"

void setup() {
  while (!Serial)
    ;

  Serial.begin(9600);
}

void loop() {
  Test::run();
}
