mrstefangrimm/Parc/Software/Src/ParcLib/Tests/Core/HidAoTest/HidAoTest.h

// Copyright (c) 2021-2023 Stefan Grimm. All rights reserved.
// Licensed under the LGPL. See LICENSE file in the project root for full license information.
//
#pragma once

#include "Core/HidAo.h"
#include "Core/Program.h"
#include "Core/Shared.h"

namespace HidAoTest {

struct FakeLogger {
  template<class T>
  void print(T) {}
  template<class T>
  void print(T, uint8_t) {}
  template<class T>
  void println(T) {}
};
}

HidAoTest::FakeLogger logger;
template<> HidAoTest::FakeLogger& parclib::Factory<HidAoTest::FakeLogger>::instance = logger;
using LoggerFac_t = parclib::Factory<HidAoTest::FakeLogger>;

namespace HidAoTest {

using namespace parclib;

struct FakeProgramStep : public ProgramStep<LoggerFac_t> {
  FakeProgramStep()
    : ProgramStep<LoggerFac_t>(10) {}

  void action(VirtualAction type, uint8_t& tick) override {
    isPlaying = type == VirtualAction::Tick;
    currentTick = tick;
  };

  bool isPlaying = false;
  uint8_t currentTick = 0;
};

// Test naming scheme: Given-When-Then

BEGIN(HidAoTest)

TEST(
  state_idle_and_no_program,
  checkRegisters,
  timeout_not_set_as_state_idle) {

  Program<LoggerFac_t> programs[NumberOfPrograms];
  memset(programs, 0, NumberOfPrograms * sizeof(Program<LoggerFac_t>));

  Messages messages;

  HidAo<LoggerFac_t, Program<LoggerFac_t>> hid(messages, programs);

  KeypadRegData hidInput(0, 1);

  messages.fromKeypadToHidQueue.push(hidInput.raw);
  hid.load();
  hid.run();

  EQ((uint8_t)0, messages.fromKeypadToHidQueue.pop());
}

TEST(
  state_idle_and_program,
  checkRegisters,
  state_execute) {

  Program<LoggerFac_t> programs[NumberOfPrograms];
  memset(programs, 0, NumberOfPrograms * sizeof(Program<LoggerFac_t>));

  Messages messages;

  HidAo<LoggerFac_t, Program<LoggerFac_t>> hid(messages, programs);

  KeypadRegData hidInput(0, 1);
  FakeProgramStep someProgramStep;
  programs[0].appendStep(&someProgramStep);

  messages.fromKeypadToHidQueue.push(hidInput.raw);

  hid.load();
  hid.run();
  // Changed from state Idle to State Execute
  EQ((uint8_t)0, messages.fromKeypadToHidQueue.pop());
  EQ((bool)false, someProgramStep.isPlaying);
  EQ((uint8_t)0, someProgramStep.currentTick);

  hid.load();
  hid.run();
  // State Execute
  EQ((uint8_t)0, messages.fromKeypadToHidQueue.pop());
  EQ((bool)true, someProgramStep.isPlaying);
  EQ((uint8_t)0, someProgramStep.currentTick);
}

END

}
